datehoer/ai_desktop_widget/output/clock/flip-clock-frames.png

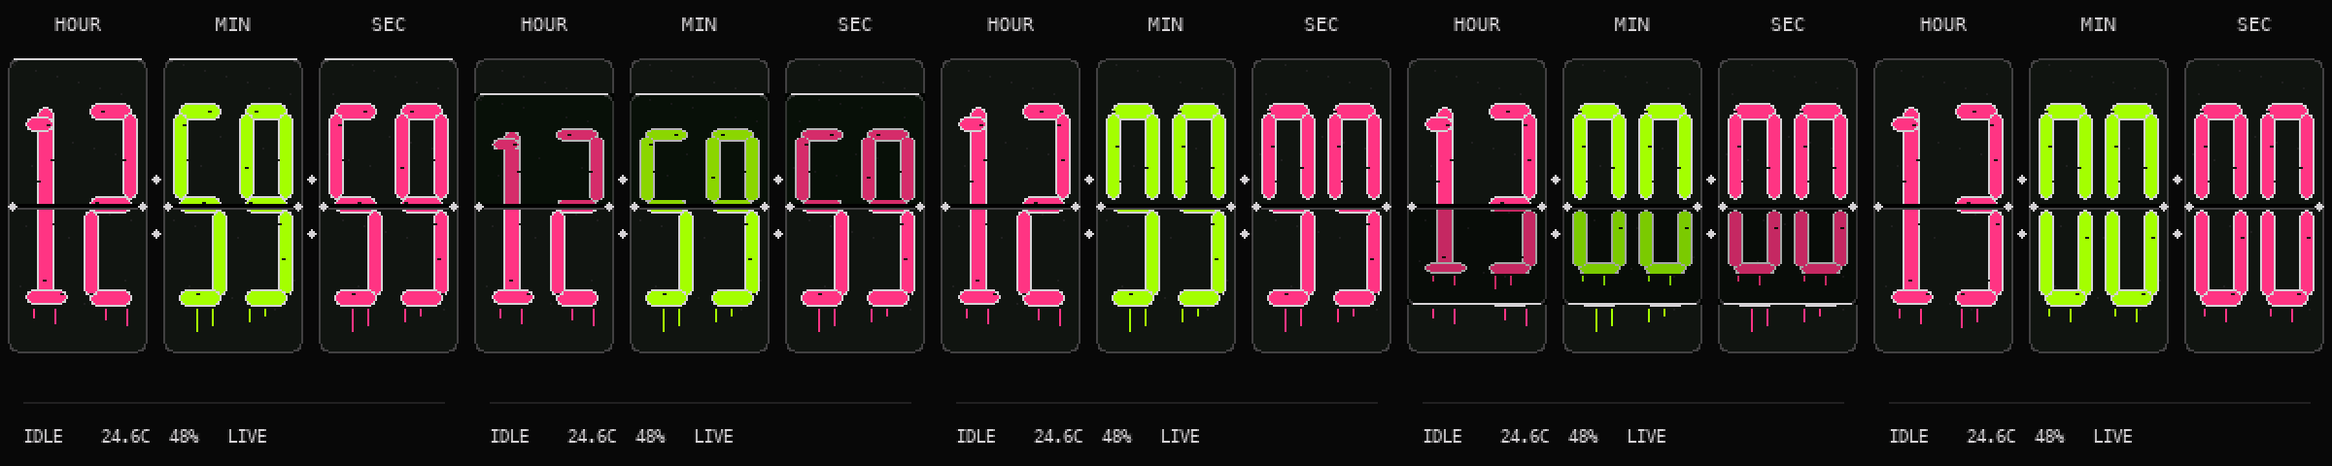
output/clock/flip-clock-frames.png
