datehoer/ai_desktop_widget/output/enclosure/back-interior-preview.png

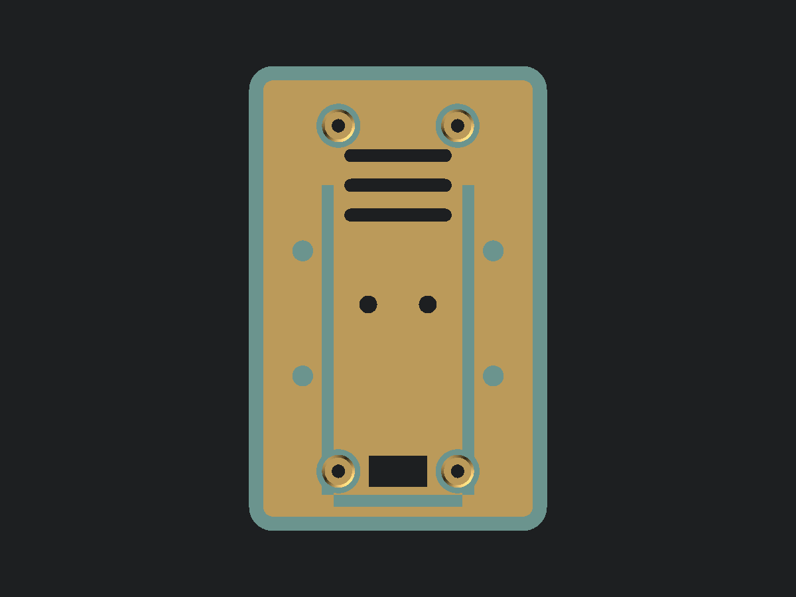
output/enclosure/back-interior-preview.png
