datehoer/ai_desktop_widget/output/enclosure/back-preview.png

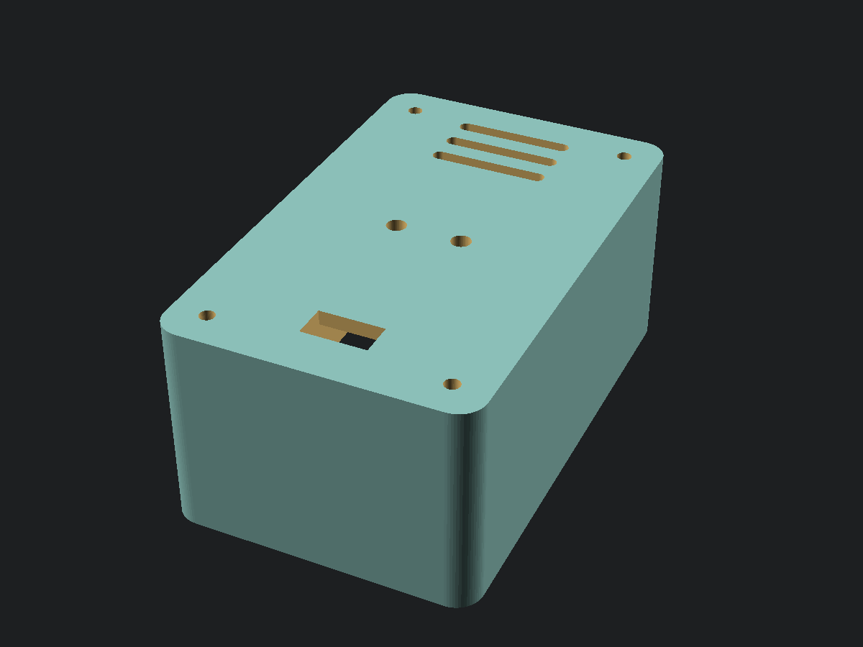
output/enclosure/back-preview.png
