datehoer/ai_desktop_widget/output/enclosure/codex-widget-enclosure-concept-v1.png

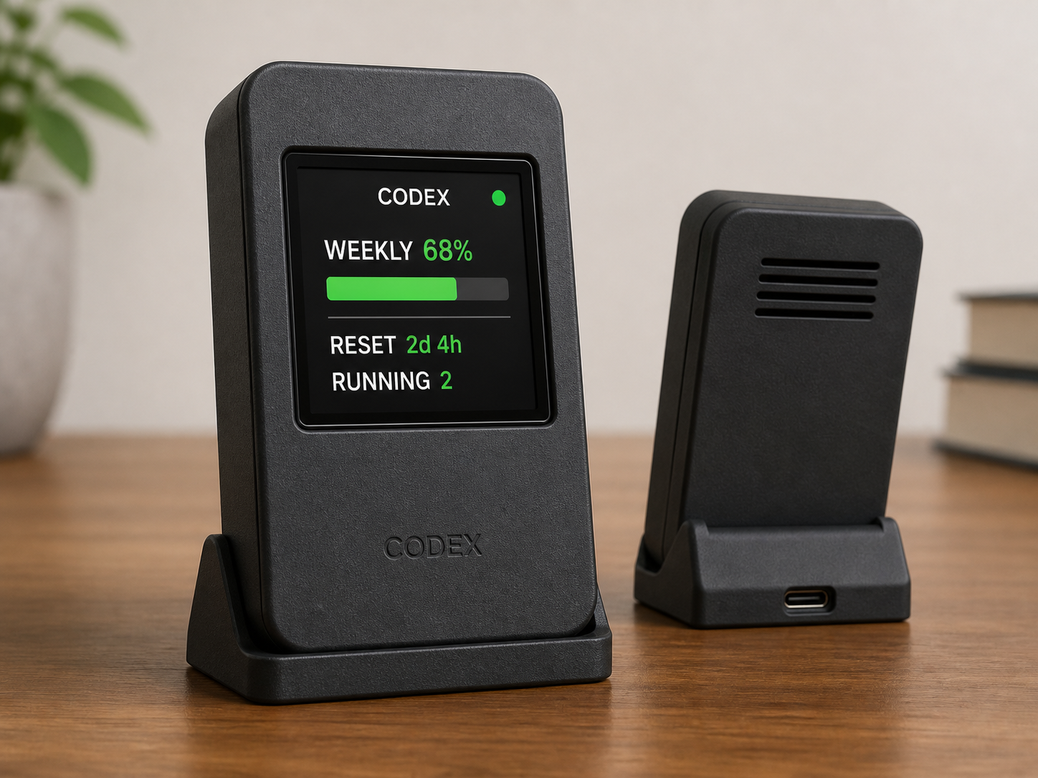
output/enclosure/codex-widget-enclosure-concept-v1.png
