datehoer/ai_desktop_widget/output/enclosure/codex-widget-graffiti-clock-v1.png

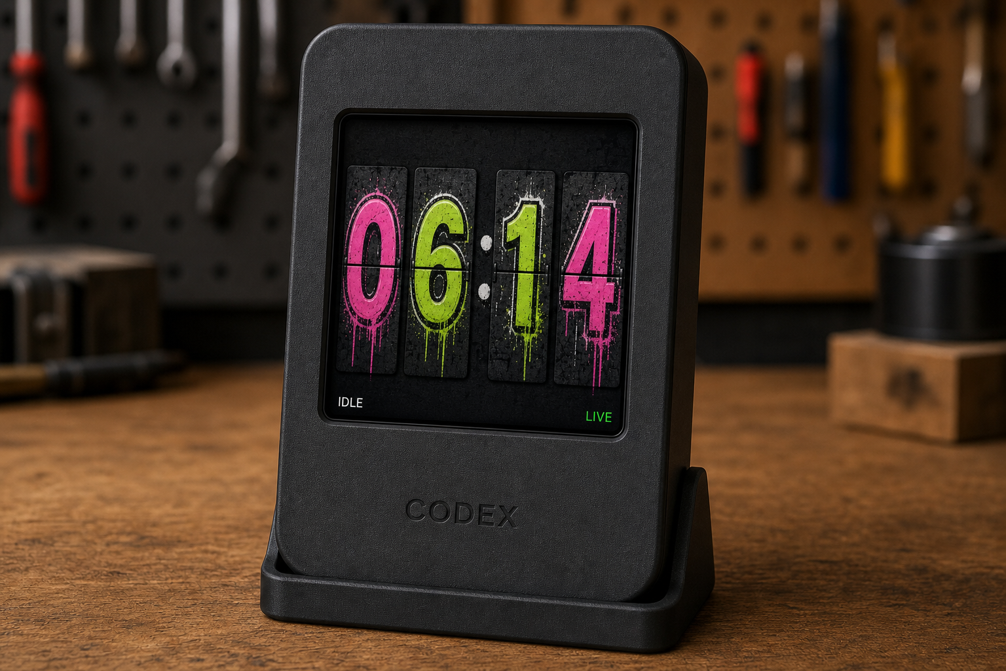
output/enclosure/codex-widget-graffiti-clock-v1.png
