datehoer/ai_desktop_widget/output/enclosure/design-option-1.png

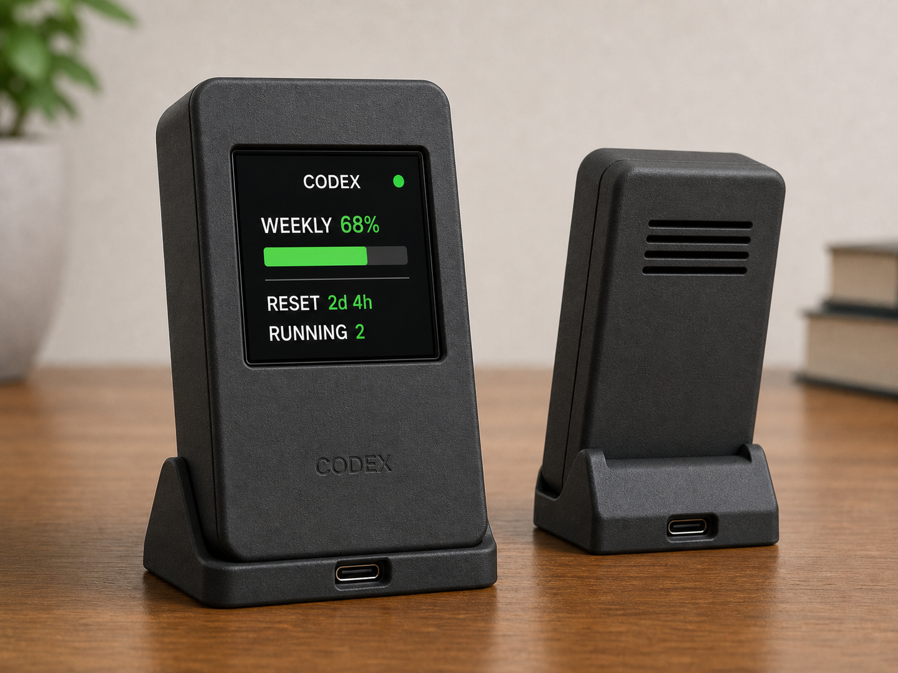
output/enclosure/design-option-1.png
