datehoer/ai_desktop_widget/output/enclosure/design-option-2.png

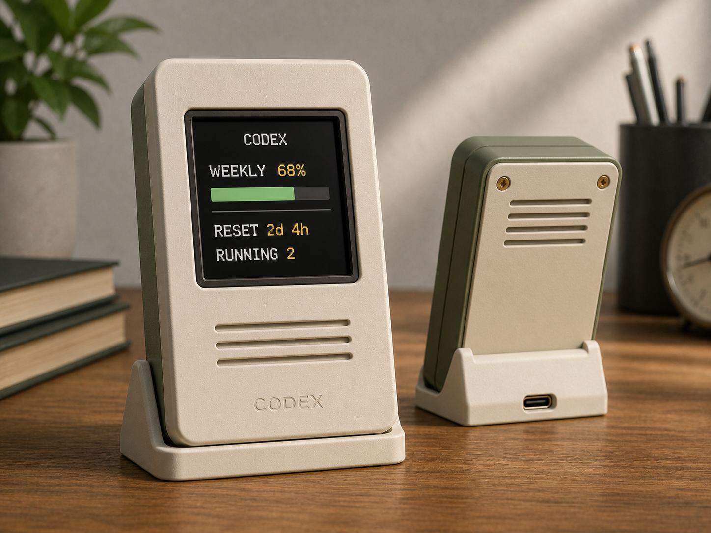
output/enclosure/design-option-2.png
