datehoer/ai_desktop_widget/output/enclosure/design-option-3.png

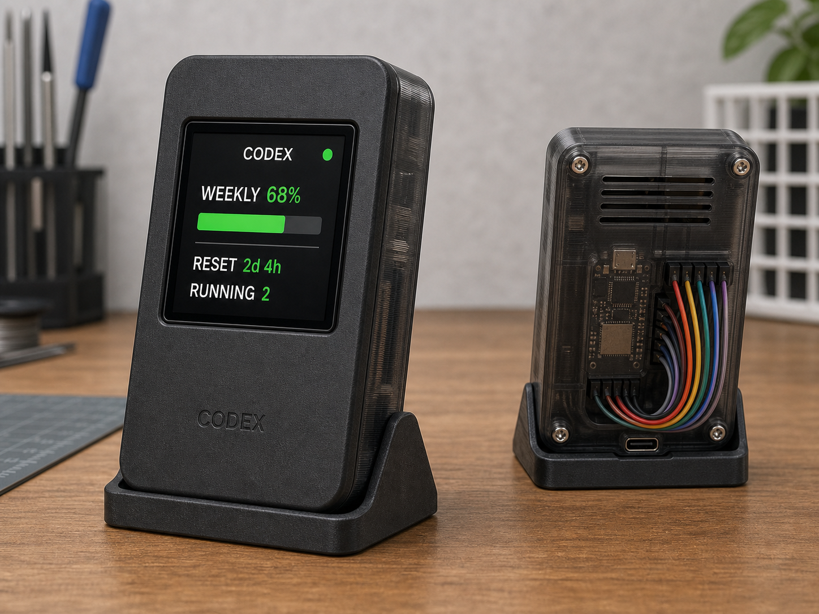
output/enclosure/design-option-3.png
