datehoer/ai_desktop_widget/output/enclosure/front-preview.png

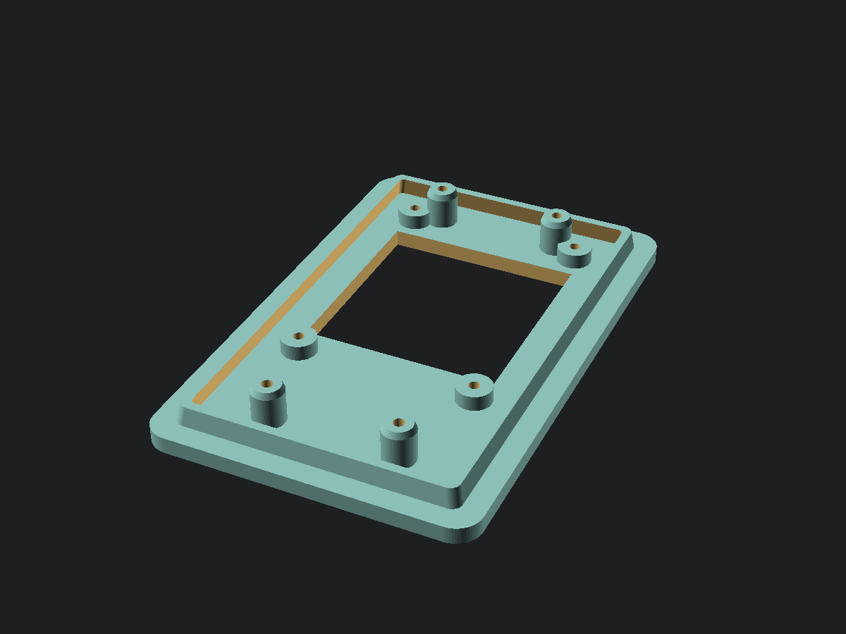
output/enclosure/front-preview.png
