datehoer/ai_desktop_widget/output/enclosure/stand-fit-preview.png

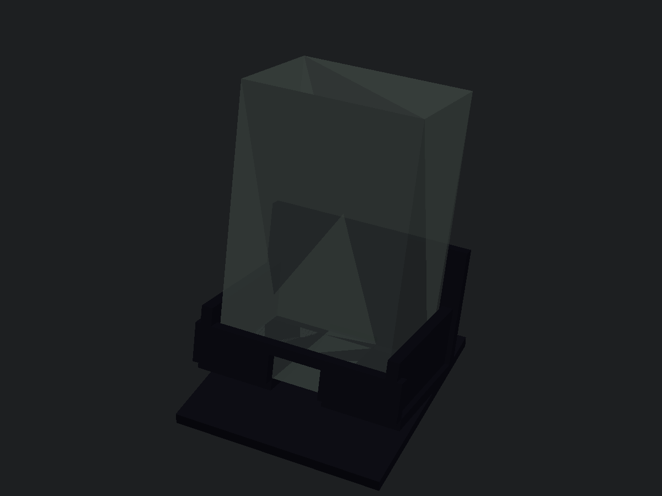
output/enclosure/stand-fit-preview.png
