datehoer/ai_desktop_widget/output/enclosure/stand-fit-side.png

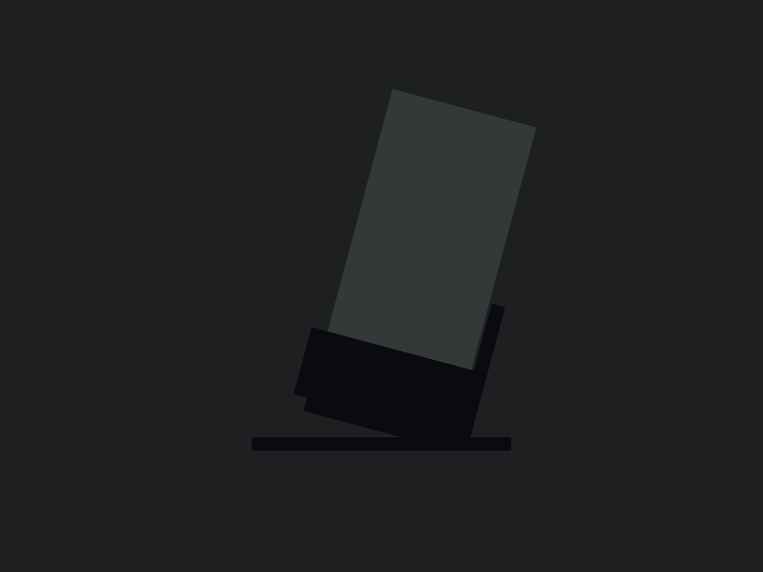
output/enclosure/stand-fit-side.png
