datehoer/ai_desktop_widget/output/enclosure/stand-preview.png

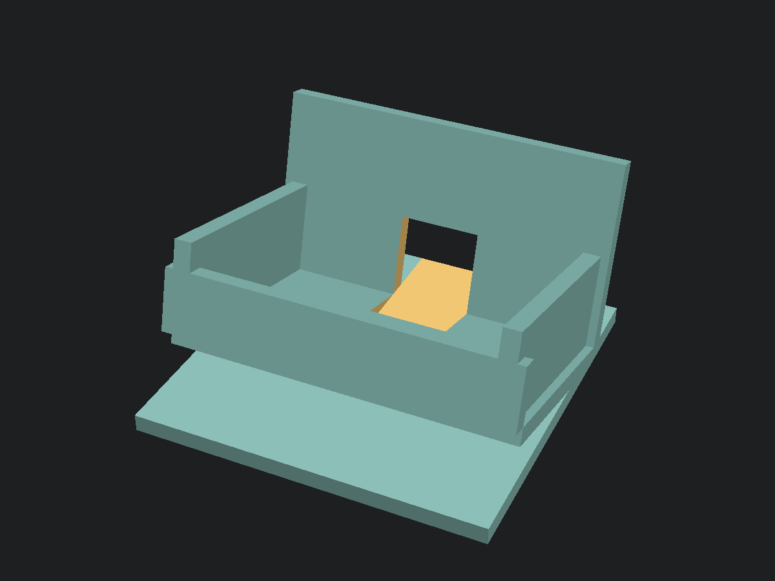
output/enclosure/stand-preview.png
