datehoer/ai_desktop_widget/output/enclosure/stand-rear-preview.png

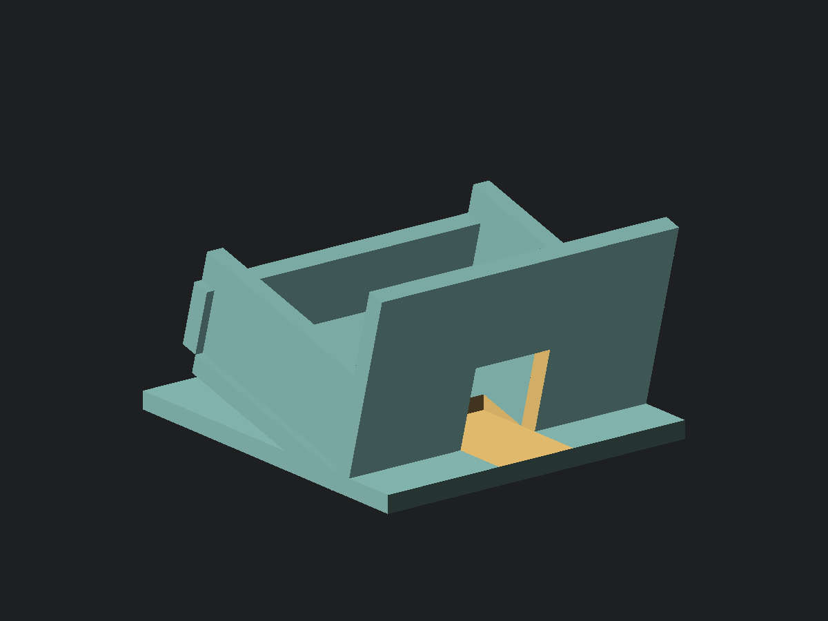
output/enclosure/stand-rear-preview.png
