datehoer/ai_desktop_widget/output/enclosure/stand-side.png

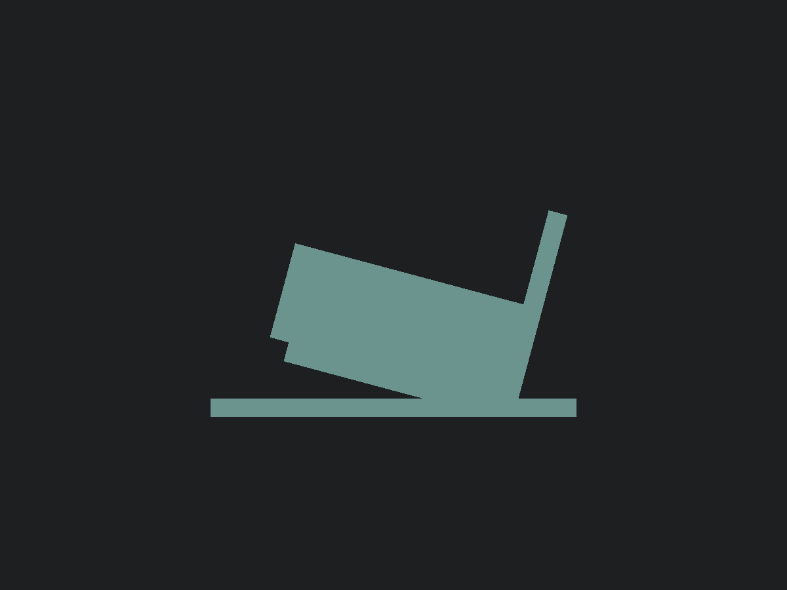
output/enclosure/stand-side.png
