datehoer/ai_desktop_widget/output/enclosure/front-black.scad

part = "front";
include <codex_widget_enclosure.scad>;
