datehoer/ai_desktop_widget/output/enclosure/stand-assembly-preview.scad

part = "stand_assembly";
include <codex_widget_enclosure.scad>;
