datehoer/ai_desktop_widget/output/enclosure/stand-black.scad

part = "stand";
include <codex_widget_enclosure.scad>;
