datehoer/ai_desktop_widget/output/enclosure/stand-fit-preview.scad

part = "stand_fit";
include <codex_widget_enclosure.scad>;
