datehoer/ai_desktop_widget/output/enclosure/stand-assembly-preview.png

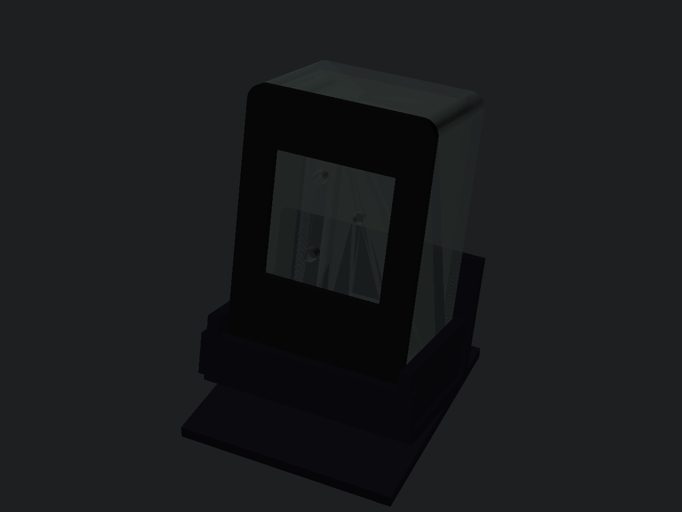
output/enclosure/stand-assembly-preview.png
