datehoer/ai_desktop_widget/output/enclosure/stand-assembly-rear.png

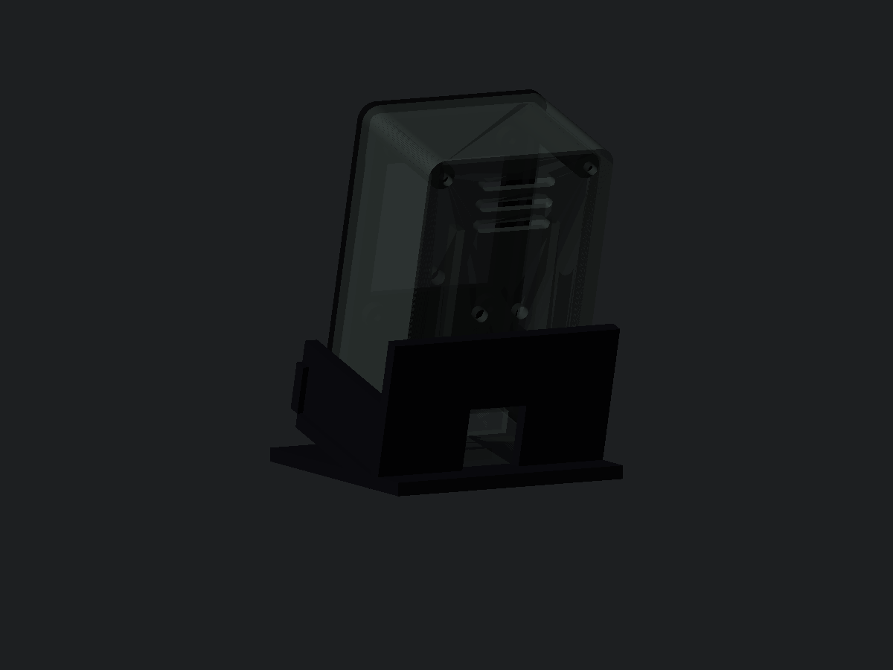
output/enclosure/stand-assembly-rear.png
